Neofoxx/HumbuckerAmplifier/Pictures/IMG_20201017_194924_107.jpg

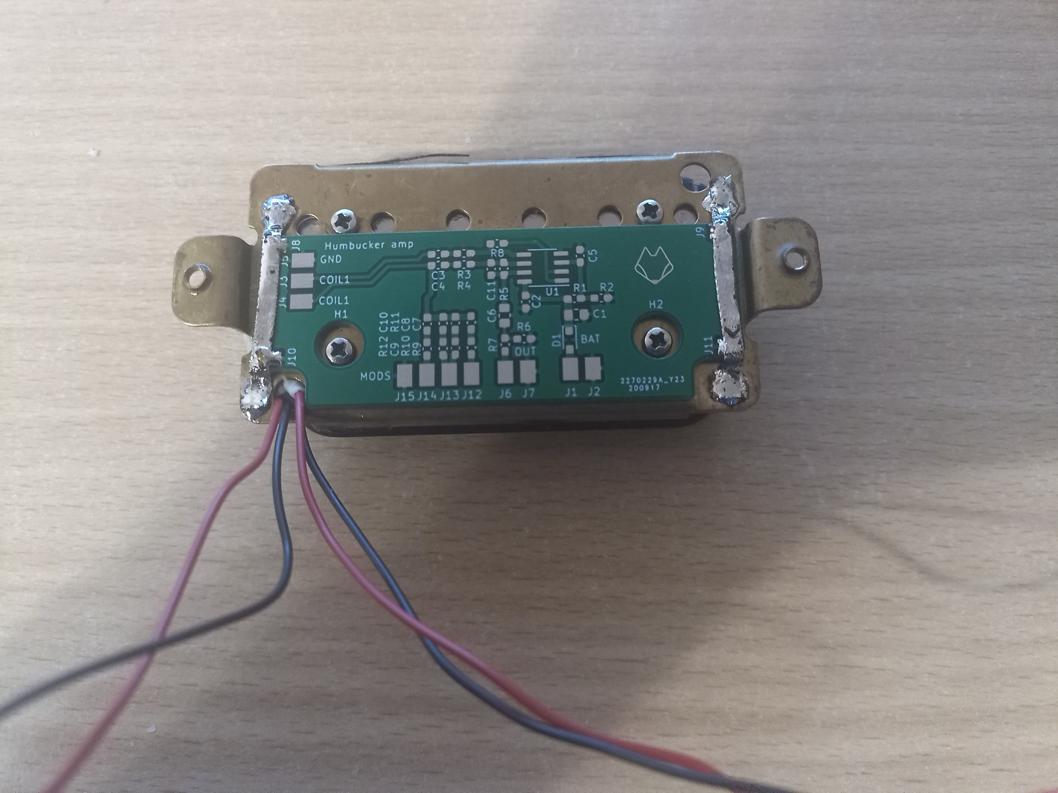
Pictures/IMG_20201017_194924_107.jpg
